Frapais/Sprig-ESP32/PCB/044.jpg

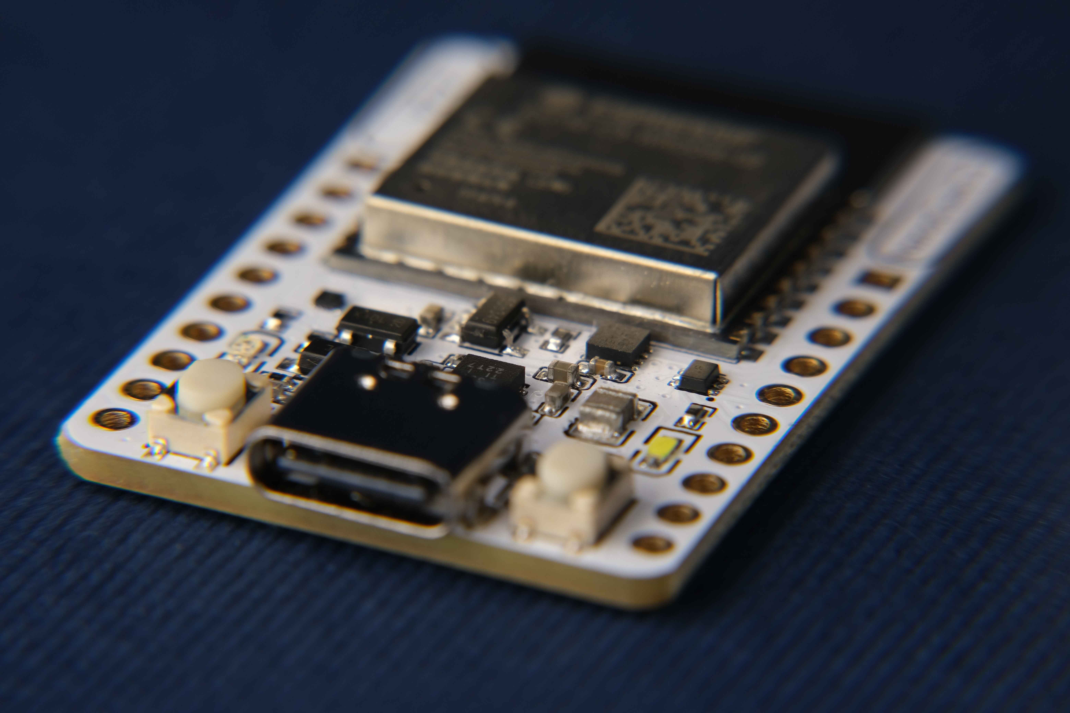
PCB/044.jpg
