Frapais/Sprig-ESP32/PCB/050.jpg

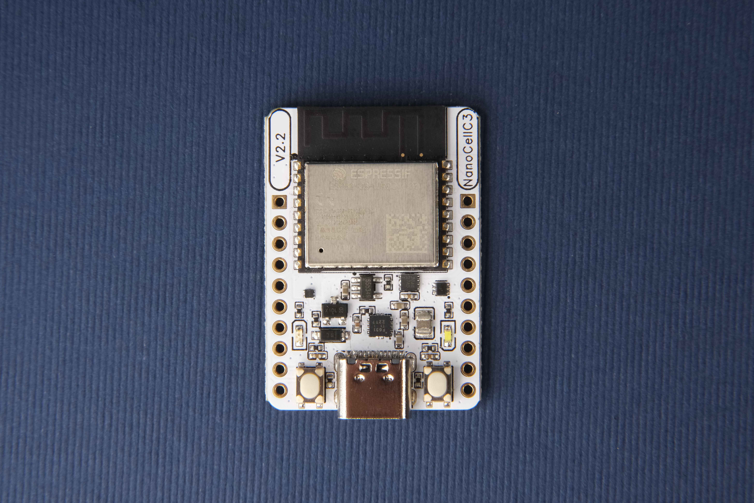
PCB/050.jpg
