Frapais/Sprig-ESP32/PCB/051.jpg

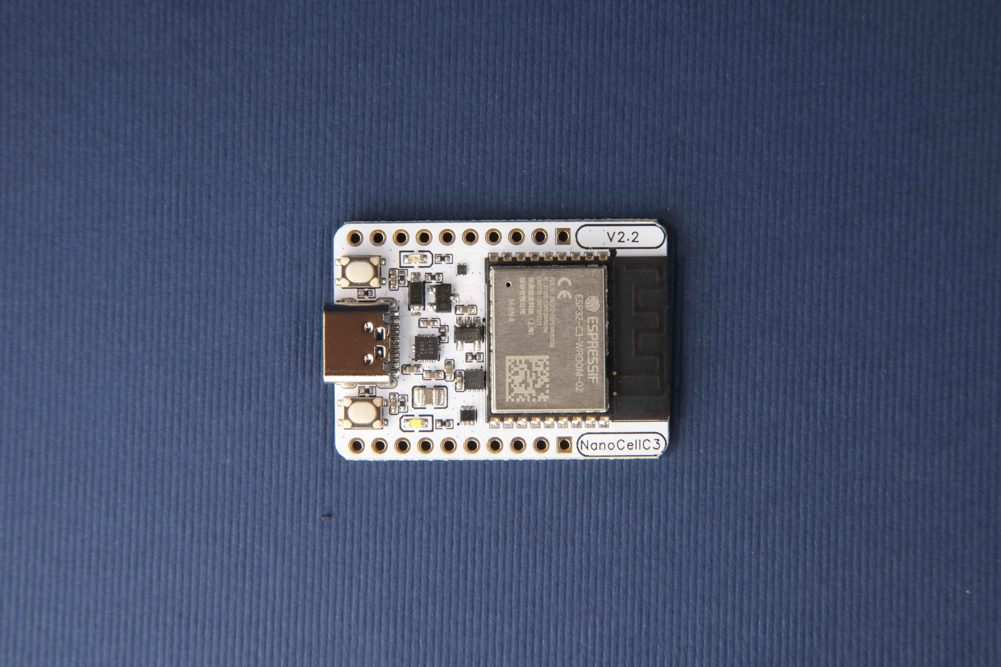
PCB/051.jpg
