Frapais/Sprig-ESP32/PCB/151.jpg

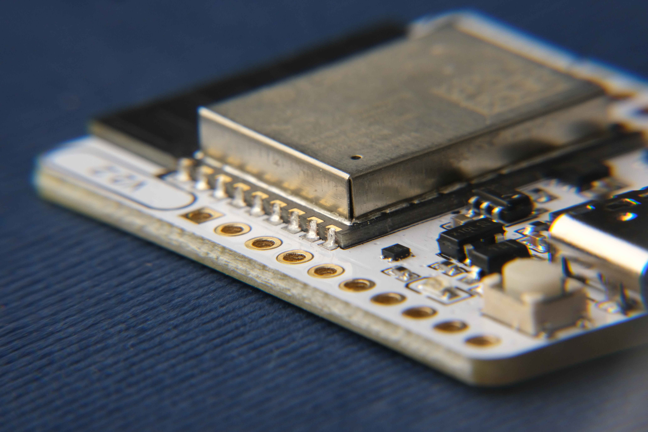
PCB/151.jpg
