Frapais/Sprig-ESP32/PCB/152.jpg

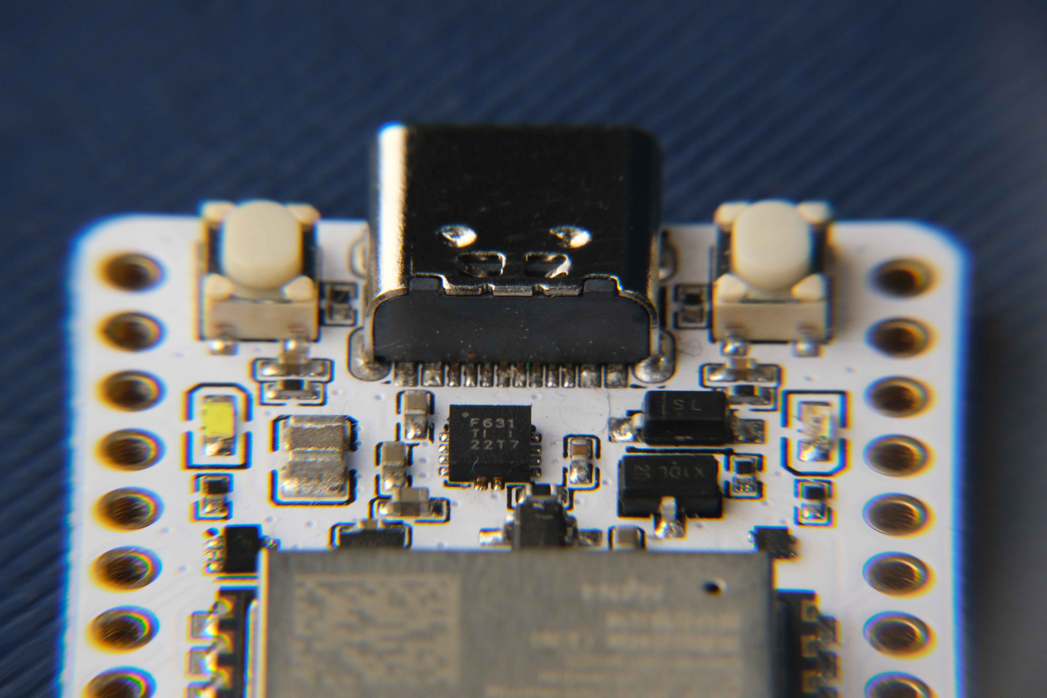
PCB/152.jpg
